bogdan-tirzioru/BusAnalizerII/AN/evb3300.pdf

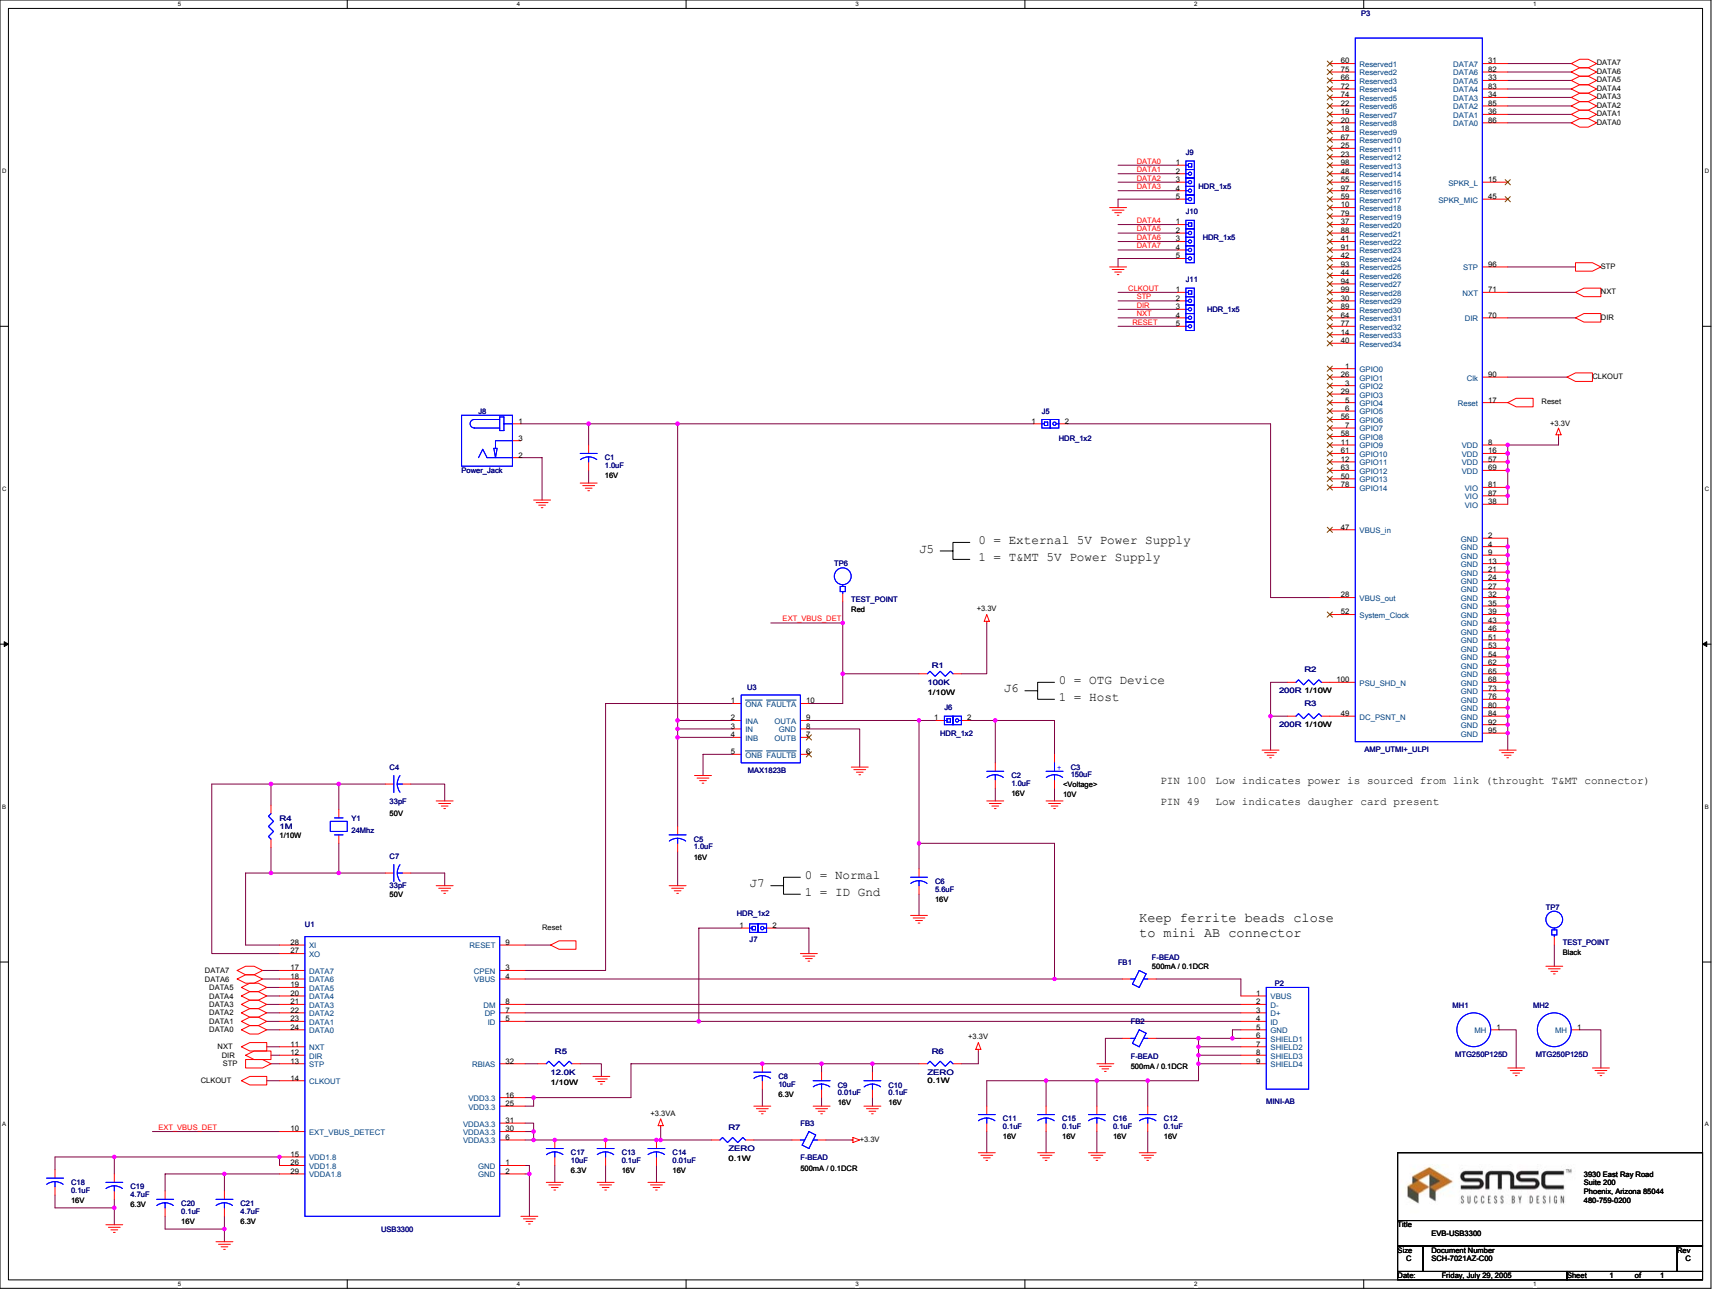
[picture p14: page 1]

PIN 100 Low indicates power is sourced from link (throught T&MT connector)
PIN 49

Low indicates daugher card present

Keep ferrite beads close
to mini AB connector

Size Size Size C C C | Document Number Document Number Document Number SCH-7021AZ-C00 SCH-7021AZ-C00 SCH-7021AZ-C00 | Rev Rev Rev C C C

Date: Date: Date: Friday, July 29, 2005 Friday, July 29, 2005 Friday, July 29, 2005 | Sheet Sheet Sheet 1 1 1 of of of 1 1 1
