bogdan-tirzioru/BusAnalizerII/firmBoard735/Core/Inc/hyperram_test.h

#ifndef HYPERRAM_TEST_H
#define HYPERRAM_TEST_H

void HyperRAM_Test_ID(void);
void HyperRAM_Test_Scope(void);
void HyperRAM_Test_Memory(void);
void HyperRAM_Test_ConfigRegisters(void);
void HyperRAM_Test_BurstStress(void);

#endif /* HYPERRAM_TEST_H */
